kongmunist/sunspot/firmware/sunspot_v1/src/config.h

// Configuration for the Sunspot 

// === SX1262 Pinout ===
#define SX1262_NSS 20
#define SX1262_DIO1 19
#define SX1262_NRST 21
#define SX1262_BUSY 18

// === Camera Pinout ===
#define CAMERA_RST 2
#define CAMERA_XCLK 3
#define CAMERA_SDA2 4
#define CAMERA_SCL2 5
#define CAMERA_D0 6
#define CAMERA_D1 7
#define CAMERA_D2 8
#define CAMERA_D3 9
#define CAMERA_D4 10
#define CAMERA_D5 11
#define CAMERA_D6 12
#define CAMERA_D7 13
#define CAMERA_PCLK 14
#define CAMERA_HREF 15
#define CAMERA_VSYNC 16
